edward62740/ot-CO2SN/Code/co2sn/config/pin_config.h

#ifndef PIN_CONFIG_H
#define PIN_CONFIG_H

// $[CMU]
// [CMU]$

// $[LFXO]
// [LFXO]$

// $[PRS.ASYNCH0]
// [PRS.ASYNCH0]$

// $[PRS.ASYNCH1]
// [PRS.ASYNCH1]$

// $[PRS.ASYNCH2]
// [PRS.ASYNCH2]$

// $[PRS.ASYNCH3]
// [PRS.ASYNCH3]$

// $[PRS.ASYNCH4]
// [PRS.ASYNCH4]$

// $[PRS.ASYNCH5]
// [PRS.ASYNCH5]$

// $[PRS.ASYNCH6]
// [PRS.ASYNCH6]$

// $[PRS.ASYNCH7]
// [PRS.ASYNCH7]$

// $[PRS.ASYNCH8]
// [PRS.ASYNCH8]$

// $[PRS.ASYNCH9]
// [PRS.ASYNCH9]$

// $[PRS.ASYNCH10]
// [PRS.ASYNCH10]$

// $[PRS.ASYNCH11]
// [PRS.ASYNCH11]$

// $[PRS.ASYNCH12]
// [PRS.ASYNCH12]$

// $[PRS.ASYNCH13]
// [PRS.ASYNCH13]$

// $[PRS.ASYNCH14]
// [PRS.ASYNCH14]$

// $[PRS.ASYNCH15]
// [PRS.ASYNCH15]$

// $[PRS.SYNCH0]
// [PRS.SYNCH0]$

// $[PRS.SYNCH1]
// [PRS.SYNCH1]$

// $[PRS.SYNCH2]
// [PRS.SYNCH2]$

// $[PRS.SYNCH3]
// [PRS.SYNCH3]$

// $[GPIO]
// [GPIO]$

// $[TIMER0]
// [TIMER0]$

// $[TIMER1]
// [TIMER1]$

// $[TIMER2]
// [TIMER2]$

// $[TIMER3]
// [TIMER3]$

// $[TIMER4]
// [TIMER4]$

// $[USART0]
// USART0 RX on PA09
#ifndef USART0_RX_PORT                          
#define USART0_RX_PORT                           gpioPortA
#endif
#ifndef USART0_RX_PIN                           
#define USART0_RX_PIN                            9
#endif

// USART0 TX on PA08
#ifndef USART0_TX_PORT                          
#define USART0_TX_PORT                           gpioPortA
#endif
#ifndef USART0_TX_PIN                           
#define USART0_TX_PIN                            8
#endif

// [USART0]$

// $[I2C1]
// I2C1 SCL on PD04
#ifndef I2C1_SCL_PORT                           
#define I2C1_SCL_PORT                            gpioPortD
#endif
#ifndef I2C1_SCL_PIN                            
#define I2C1_SCL_PIN                             4
#endif

// I2C1 SDA on PD03
#ifndef I2C1_SDA_PORT                           
#define I2C1_SDA_PORT                            gpioPortD
#endif
#ifndef I2C1_SDA_PIN                            
#define I2C1_SDA_PIN                             3
#endif

// [I2C1]$

// $[EUSART1]
// [EUSART1]$

// $[KEYSCAN]
// [KEYSCAN]$

// $[LETIMER0]
// [LETIMER0]$

// $[ACMP0]
// [ACMP0]$

// $[ACMP1]
// [ACMP1]$

// $[VDAC0]
// [VDAC0]$

// $[VDAC1]
// [VDAC1]$

// $[PCNT0]
// [PCNT0]$

// $[HFXO0]
// [HFXO0]$

// $[I2C0]
// I2C0 SCL on PB01
#ifndef I2C0_SCL_PORT                           
#define I2C0_SCL_PORT                            gpioPortB
#endif
#ifndef I2C0_SCL_PIN                            
#define I2C0_SCL_PIN                             1
#endif

// I2C0 SDA on PB00
#ifndef I2C0_SDA_PORT                           
#define I2C0_SDA_PORT                            gpioPortB
#endif
#ifndef I2C0_SDA_PIN                            
#define I2C0_SDA_PIN                             0
#endif

// [I2C0]$

// $[EUSART0]
// [EUSART0]$

// $[PTI]
// [PTI]$

// $[MODEM]
// [MODEM]$

// $[CUSTOM_PIN_NAME]
// [CUSTOM_PIN_NAME]$

#endif // PIN_CONFIG_H

// $[IADC0]
// [IADC0]$
