edward62740/ot-CO2SN/Code/co2sn/app_thread.cpp

#include "app_thread.h"
#include "app_main.h"
#include <stdio.h>
#include <string.h>
#include <assert.h>

#include <openthread/cli.h>
#include <openthread/dataset_ftd.h>
#include <openthread/instance.h>
#include <openthread/message.h>
#include <openthread/thread.h>
#include <openthread/udp.h>
#include <openthread/platform/logging.h>
#include <common/code_utils.hpp>
#include <common/logging.hpp>



#include "sl_component_catalog.h"
#ifdef SL_CATALOG_POWER_MANAGER_PRESENT
#include "sl_power_manager.h"
#endif



otInstance *otGetInstance(void);

constexpr static bool LOW_POWER_MODE = true;

void sleepyInit(uint32_t poll_period)
{
    otError error;

    otLinkModeConfig config;
    SuccessOrExit(error = otLinkSetPollPeriod(otGetInstance(), poll_period));

    config.mRxOnWhenIdle = false;
    config.mDeviceType   = 0;
    config.mNetworkData  = 0;
    SuccessOrExit(error = otThreadSetLinkMode(otGetInstance(), config));

exit:
    return;
}

/*
 * Callback from sl_ot_is_ok_to_sleep to check if it is ok to go to sleep.
 */
inline bool efr32AllowSleepCallback(void)
{
    return LOW_POWER_MODE;
}

/*
 * Override default network settings, such as panid, so the devices can join a network
 */
void setNetworkConfiguration(void)
{
    static char          aNetworkName[] = "";
    otError              error;
    otOperationalDataset aDataset;

    memset(&aDataset, 0, sizeof(otOperationalDataset));

    /*
     * Fields that can be configured in otOperationDataset to override defaults:
     *     Network Name, Mesh Local Prefix, Extended PAN ID, PAN ID, Delay Timer,
     *     Channel, Channel Mask Page 0, Network Key, PSKc, Security Policy
     */
    //aDataset.mActiveTimestamp.mSeconds             = 1;
    aDataset.mComponents.mIsActiveTimestampPresent = true;

    /* Set Channel to 15 */
    aDataset.mChannel                      = 15;
    aDataset.mComponents.mIsChannelPresent = true;

    /* Set Pan ID to 2222 */
    aDataset.mPanId                      = (otPanId);
    aDataset.mComponents.mIsPanIdPresent = true;

    /* Set Extended Pan ID to C0DE1AB5C0DE1AB5 */
    uint8_t extPanId[OT_EXT_PAN_ID_SIZE] = {};
    memcpy(aDataset.mExtendedPanId.m8, extPanId, sizeof(aDataset.mExtendedPanId));
    aDataset.mComponents.mIsExtendedPanIdPresent = true;

    /* Set network key to 1234C0DE1AB51234C0DE1AB51234C0DE */
    uint8_t key[OT_NETWORK_KEY_SIZE] = { };
    memcpy(aDataset.mNetworkKey.m8, key, sizeof(aDataset.mNetworkKey));
    aDataset.mComponents.mIsNetworkKeyPresent = true;

    /* Set Network Name to SleepyEFR32 */
    size_t length = strlen(aNetworkName);
    assert(length <= OT_NETWORK_NAME_MAX_SIZE);
    memcpy(aDataset.mNetworkName.m8, aNetworkName, length);
    aDataset.mComponents.mIsNetworkNamePresent = true;

    /* Set the Active Operational Dataset to this dataset */
    error = otDatasetSetActive(otGetInstance(), &aDataset);
    if (error != OT_ERROR_NONE)
    {
        otCliOutputFormat("otDatasetSetActive failed with: %d, %s\r\n", error, otThreadErrorToString(error));
        return;
    }
}
