edward62740/ot-CO2SN/Code/co2sn/sensors/scd4x/sensirion_i2c_hal.c

/*
 * Copyright (c) 2018, Sensirion AG
 * All rights reserved.
 *
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
 * * Neither the name of Sensirion AG nor the names of its
 *   contributors may be used to endorse or promote products derived from
 *   this software without specific prior written permission.
 *
 * THIS SOFTWARE IS PROVIDED BY THE COPYRIGHT HOLDERS AND CONTRIBUTORS "AS IS"
 * AND ANY EXPRESS OR IMPLIED WARRANTIES, INCLUDING, BUT NOT LIMITED TO, THE
 * IMPLIED WARRANTIES OF MERCHANTABILITY AND FITNESS FOR A PARTICULAR PURPOSE
 * ARE DISCLAIMED. IN NO EVENT SHALL THE COPYRIGHT HOLDER OR CONTRIBUTORS BE
 * LIABLE FOR ANY DIRECT, INDIRECT, INCIDENTAL, SPECIAL, EXEMPLARY, OR
 * CONSEQUENTIAL DAMAGES (INCLUDING, BUT NOT LIMITED TO, PROCUREMENT OF
 * SUBSTITUTE GOODS OR SERVICES; LOSS OF USE, DATA, OR PROFITS; OR BUSINESS
 * INTERRUPTION) HOWEVER CAUSED AND ON ANY THEORY OF LIABILITY, WHETHER IN
 * CONTRACT, STRICT LIABILITY, OR TORT (INCLUDING NEGLIGENCE OR OTHERWISE)
 * ARISING IN ANY WAY OUT OF THE USE OF THIS SOFTWARE, EVEN IF ADVISED OF THE
 * POSSIBILITY OF SUCH DAMAGE.
 */

#include "sensirion_i2c_hal.h"
#include "sensirion_common.h"
#include "sensirion_config.h"
#include "sl_i2cspm.h"
#include "sl_sleeptimer.h"
/*
 * INSTRUCTIONS
 * ============
 *
 * Implement all functions where they are marked as IMPLEMENT.
 * Follow the function specification in the comments.
 */

/**
 * Select the current i2c bus by index.
 * All following i2c operations will be directed at that bus.
 *
 * THE IMPLEMENTATION IS OPTIONAL ON SINGLE-BUS SETUPS (all sensors on the same
 * bus)
 *
 * @param bus_idx   Bus index to select
 * @returns         0 on success, an error code otherwise
 */
int16_t sensirion_i2c_hal_select_bus(uint8_t bus_idx) {
    /* TODO:IMPLEMENT or leave empty if all sensors are located on one single
     * bus
     */
    return NOT_IMPLEMENTED_ERROR;
}

/**
 * Initialize all hard- and software components that are needed for the I2C
 * communication.
 */
void sensirion_i2c_hal_init(void) {
    /* TODO:IMPLEMENT */
}

/**
 * Release all resources initialized by sensirion_i2c_hal_init().
 */
void sensirion_i2c_hal_free(void) {
    /* TODO:IMPLEMENT or leave empty if no resources need to be freed */
}

/**
 * Execute one read transaction on the I2C bus, reading a given number of bytes.
 * If the device does not acknowledge the read command, an error shall be
 * returned.
 *
 * @param address 7-bit I2C address to read from
 * @param data    pointer to the buffer where the data is to be stored
 * @param count   number of bytes to read from I2C and store in the buffer
 * @returns 0 on success, error code otherwise
 */
int8_t sensirion_i2c_hal_read(uint8_t address, uint8_t* data, uint16_t count) {

	I2C_TransferSeq_TypeDef i2cTransfer;
	I2C_TransferReturn_TypeDef result;

	// Initialize I2C transfer
	i2cTransfer.addr = address << 1;
	i2cTransfer.flags = I2C_FLAG_READ; // must write target address before reading
	i2cTransfer.buf[0].data = data;
	i2cTransfer.buf[0].len = count;

	result = I2CSPM_Transfer(I2C0, &i2cTransfer);

	return 0;
}

/**
 * Execute one write transaction on the I2C bus, sending a given number of
 * bytes. The bytes in the supplied buffer must be sent to the given address. If
 * the slave device does not acknowledge any of the bytes, an error shall be
 * returned.
 *
 * @param address 7-bit I2C address to write to
 * @param data    pointer to the buffer containing the data to write
 * @param count   number of bytes to read from the buffer and send over I2C
 * @returns 0 on success, error code otherwise
 */
int8_t sensirion_i2c_hal_write(uint8_t address, const uint8_t* data,
                               uint16_t count) {
    I2C_TransferSeq_TypeDef i2cTransfer;
    I2C_TransferReturn_TypeDef result;

    // Initialize I2C transfer
    i2cTransfer.addr = address << 1 ;
    i2cTransfer.flags = I2C_FLAG_WRITE;
    i2cTransfer.buf[0].data = data;
    i2cTransfer.buf[0].len = count;

    result = I2CSPM_Transfer(I2C0, &i2cTransfer);
    return 0;
}

/**
 * Sleep for a given number of microseconds. The function should delay the
 * execution for at least the given time, but may also sleep longer.
 *
 * Despite the unit, a <10 millisecond precision is sufficient.
 *
 * @param useconds the sleep time in microseconds
 */
void sensirion_i2c_hal_sleep_usec(uint32_t useconds) {
	if(useconds > 1000) return;
    sl_sleeptimer_delay_millisecond(useconds/1000);
}
