edward62740/ot-CO2SN/Code/co2sn/app_thread.h

#ifndef APP_THREAD_H_
#define APP_THREAD_H_

#ifdef __cplusplus
extern "C"
{
#endif

#include "stdint.h"

    void sleepyInit(uint32_t poll_period);
    void setNetworkConfiguration(void);

#ifdef __cplusplus
}
#endif /* __cplusplus */

#endif /* APP_THREAD_H_ */
