edward62740/ot-CO2SN/Code/co2sn/autogen/sl_component_catalog.h

#ifndef SL_COMPONENT_CATALOG_H
#define SL_COMPONENT_CATALOG_H

// APIs present in project
#define SL_CATALOG_DEVICE_INIT_NVIC_PRESENT
#define SL_CATALOG_EMLIB_CORE_PRESENT
#define SL_CATALOG_EMLIB_CORE_DEBUG_CONFIG_PRESENT
#define SL_CATALOG_MPU_PRESENT
#define SL_CATALOG_NVM3_PRESENT
#define SL_CATALOG_OPENTHREAD_CLI_PRESENT
#define SL_CATALOG_OPENTHREAD_STACK_PRESENT
#define SL_CATALOG_POWER_MANAGER_PRESENT
#define SL_CATALOG_PSA_CRYPTO_PRESENT
#define SL_CATALOG_RAIL_LIB_PRESENT
#define SL_CATALOG_RAIL_UTIL_PTI_PRESENT
#define SL_CATALOG_SE_MANAGER_PRESENT
#define SL_CATALOG_SECURITY_MANAGER_PRESENT
#define SL_CATALOG_SLEEPTIMER_PRESENT
#define SL_CATALOG_SLI_PROTOCOL_CRYPTO_PRESENT
#define SL_CATALOG_UARTDRV_USART_PRESENT

#endif // SL_COMPONENT_CATALOG_H
